jimmy900909/Commutator-motorization-counterbalance-sys/parts/motorization/magholder2.SLDPRT

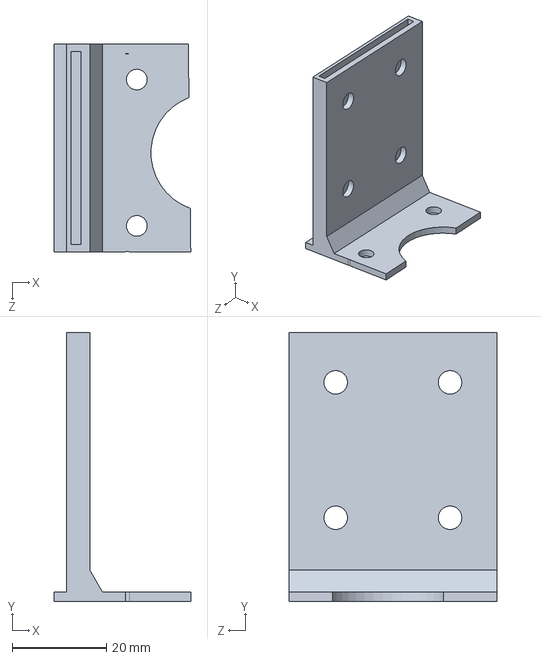
[picture p17: CAD file, 2025-11-25]
parts/motorization/magholder2.SLDPRT
28.9 x 57.0 x 44.0 mm
