jimmy900909/Commutator-motorization-counterbalance-sys/parts/counterbalance/Ver1/batteryholder.SLDPRT

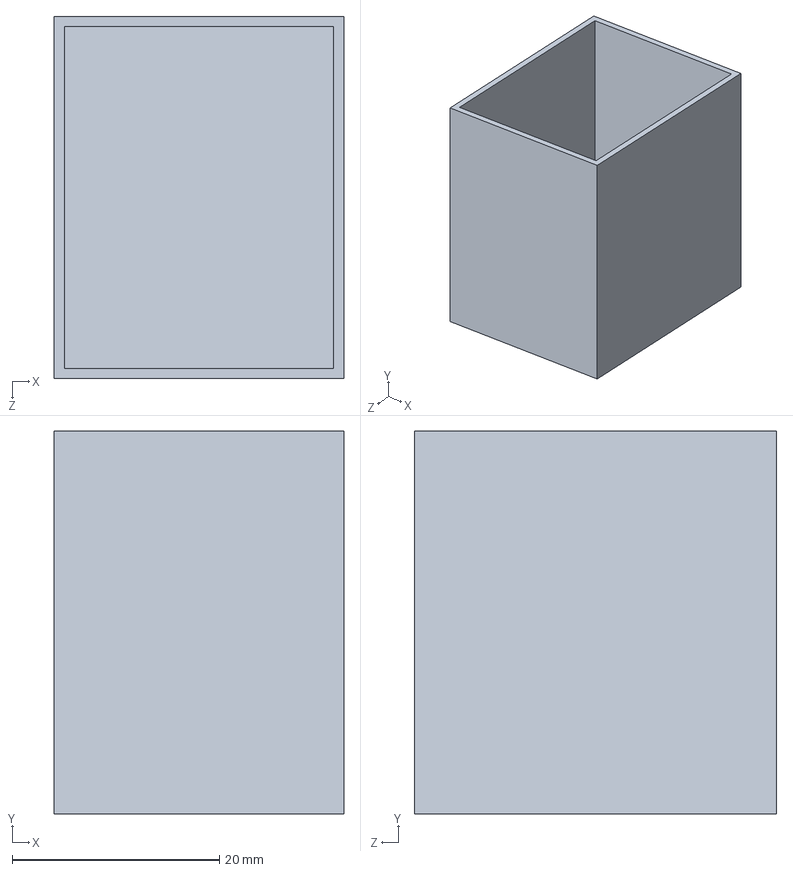
[picture p18: CAD file, 2025-11-25]
parts/counterbalance/Ver1/batteryholder.SLDPRT
28.0 x 37.0 x 35.0 mm
