jimmy900909/Commutator-motorization-counterbalance-sys/parts/motorization/magholder..SLDPRT

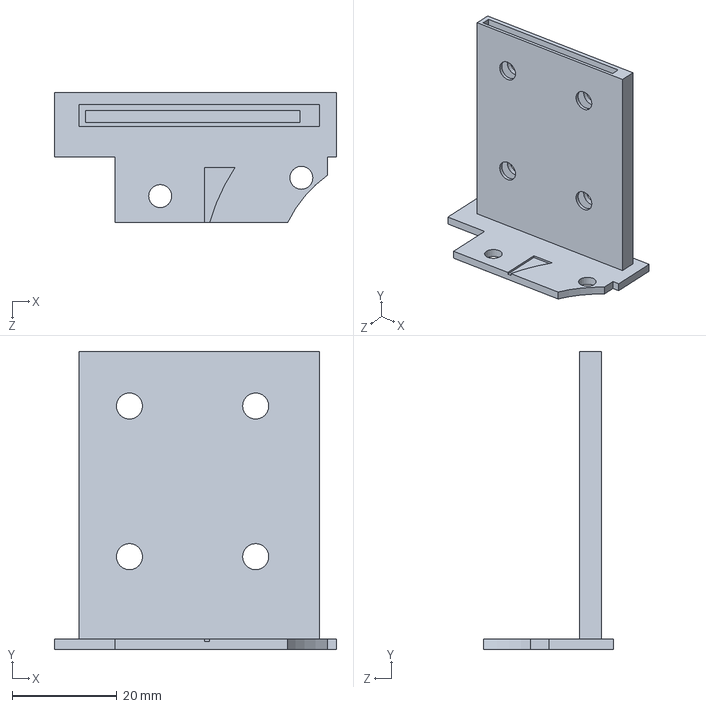
[picture p19: CAD file, 2025-11-25]
parts/motorization/magholder..SLDPRT
54.0 x 57.0 x 24.9 mm
