jimmy900909/Commutator-motorization-counterbalance-sys/parts/counterbalance/Ver1/downconnectube.STL

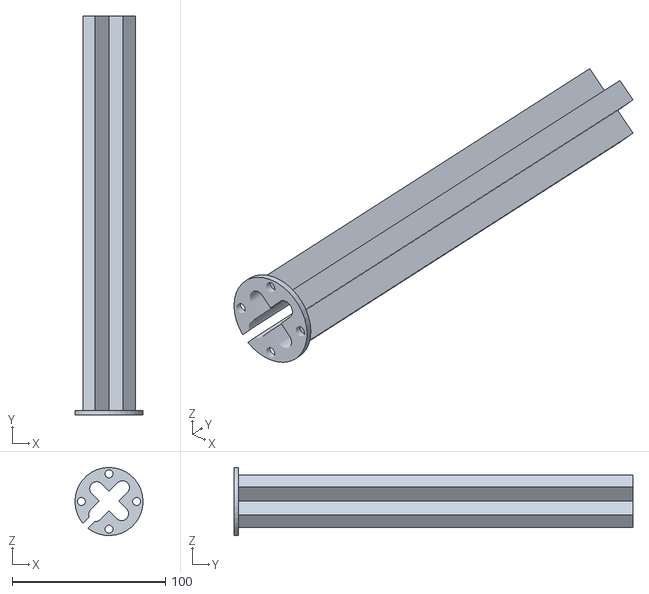
[picture p20: CAD file, 2025-11-25]
parts/counterbalance/Ver1/downconnectube.STL
44.4 x 260.0 x 44.4
