jimmy900909/Commutator-motorization-counterbalance-sys/parts/counterbalance/Ver1/零件1.SLDPRT

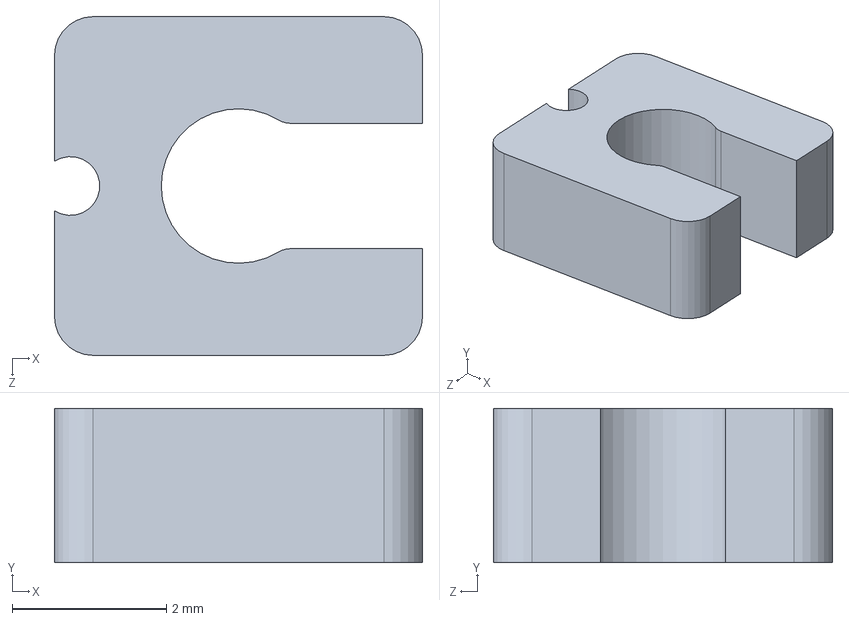
[picture p21: CAD file, 2025-11-25]
parts/counterbalance/Ver1/零件1.SLDPRT
4.78 x 2.00 x 4.40 mm
