jimmy900909/Commutator-motorization-counterbalance-sys/parts/counterbalance/Ver1/connector.SLDPRT

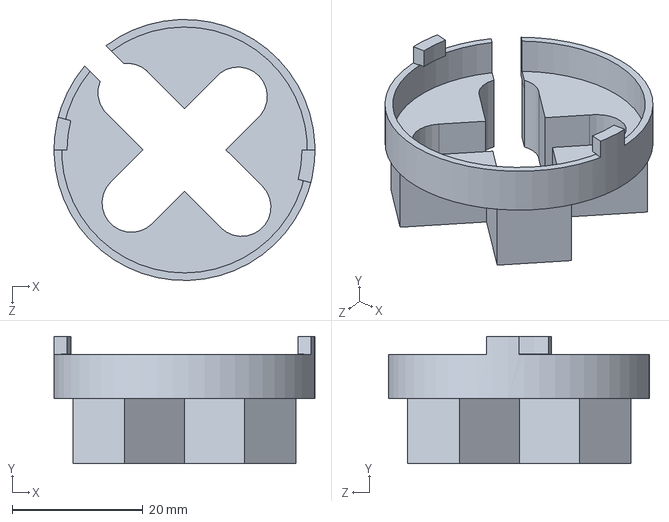
[picture p22: CAD file, 2025-11-25]
parts/counterbalance/Ver1/connector.SLDPRT
40.0 x 19.5 x 40.0 mm
