jimmy900909/Commutator-motorization-counterbalance-sys/parts/motorization/combine_lifted.SLDPRT

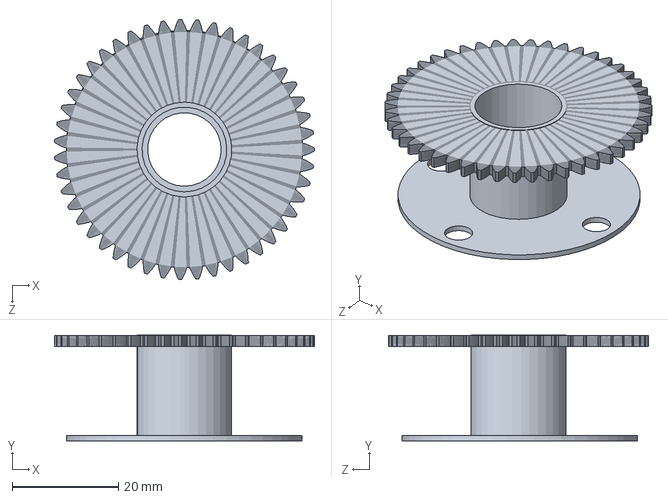
[picture p23: CAD file, 2025-08-10]
parts/motorization/combine_lifted.SLDPRT
49.0 x 19.9 x 49.0 mm
