jimmy900909/Commutator-motorization-counterbalance-sys/parts/counterbalance/Ver1/pulley_motor.SLDPRT

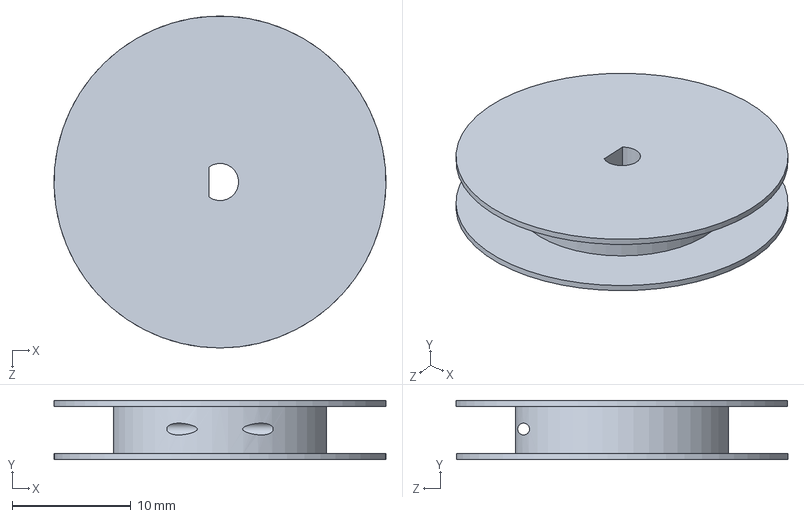
[picture p24: CAD file, 2025-08-11]
parts/counterbalance/Ver1/pulley_motor.SLDPRT
28.0 x 5.00 x 28.0 mm
