jimmy900909/Commutator-motorization-counterbalance-sys/parts/counterbalance/Ver1/pulley_fixed.SLDPRT

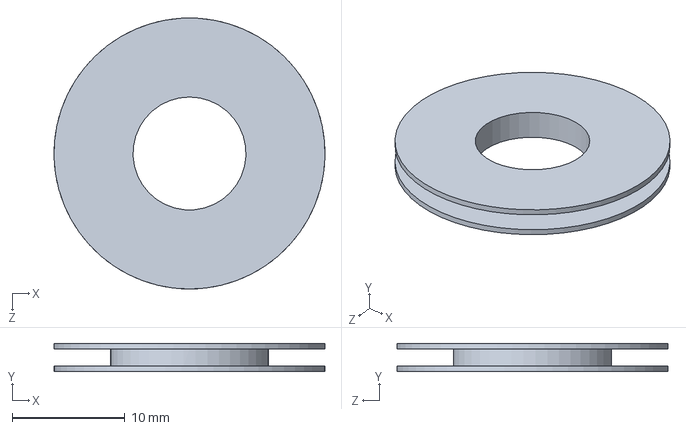
[picture p25: CAD file, 2025-08-11]
parts/counterbalance/Ver1/pulley_fixed.SLDPRT
24.0 x 2.50 x 24.0 mm
